agmlego/Creekfleet_Timer/firmware/CreekFleet_Timer/src/horn.h

uint8_t CREEKFLEET_NUM_HORNS = 44;
uint64_t CREEKFLEET_HORN_TIMES[] = {
	0,
	750,
	1125,
	1875,
	2250,
	3000,
	60000,
	60750,
	61125,
	61875,
	90000,
	90750,
	91125,
	91525,
	91725,
	92125,
	92325,
	92725,
	120000,
	120750,
	150000,
	150400,
	150600,
	151000,
	151200,
	151600,
	160000,
	160400,
	160600,
	161000,
	170000,
	170400,
	175000,
	175400,
	176000,
	176400,
	177000,
	177400,
	178000,
	178400,
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
};
bool CREEKFLEET_HORN_COMMANDS[] = {
	true,
	false,
	true,
	false,
	true,
	false,
	true,
	false,
	true,
	false,
	true,
	false,
	true,
	false,
	true,
	false,
	true,
	false,
	true,
	false,
	true,
	false,
	true,
	false,
	true,
	false,
	true,
	false,
	true,
	false,
	true,
	false,
	true,
	false,
	true,
	false,
	true,
	false,
	true,
	false,
	true,
	false,
	true,
	false
};
uint8_t ISAF_NUM_HORNS = 8;
uint64_t ISAF_HORN_TIMES[] = {
	0,
	400,
	60000,
	60400,
	240000,
	240750,
	300000,
	300400
};
bool ISAF_HORN_COMMANDS[] = {
	true,
	false,
	true,
	false,
	true,
	false,
	true,
	false
};
